shenshang521/ELEC70132_Group5_Environment-sensor/src/main/secrets.h

#ifndef SECRETS_H
#define SECRETS_H

// ==========================================
// MODULE : WiFi Configuration
// ------------------------------------------
// This section defines the network credentials required for the ESP32 
// to connect to the local router. 
// ==========================================
const char* ssid = "YOUR_WIFI_SSID";      
const char* password = "YOUR_WIFI_PASSWORD"; 

#endif
